Inventoteca/Alarma_Mochila/capturas y fotos/abrir manage pallete.png

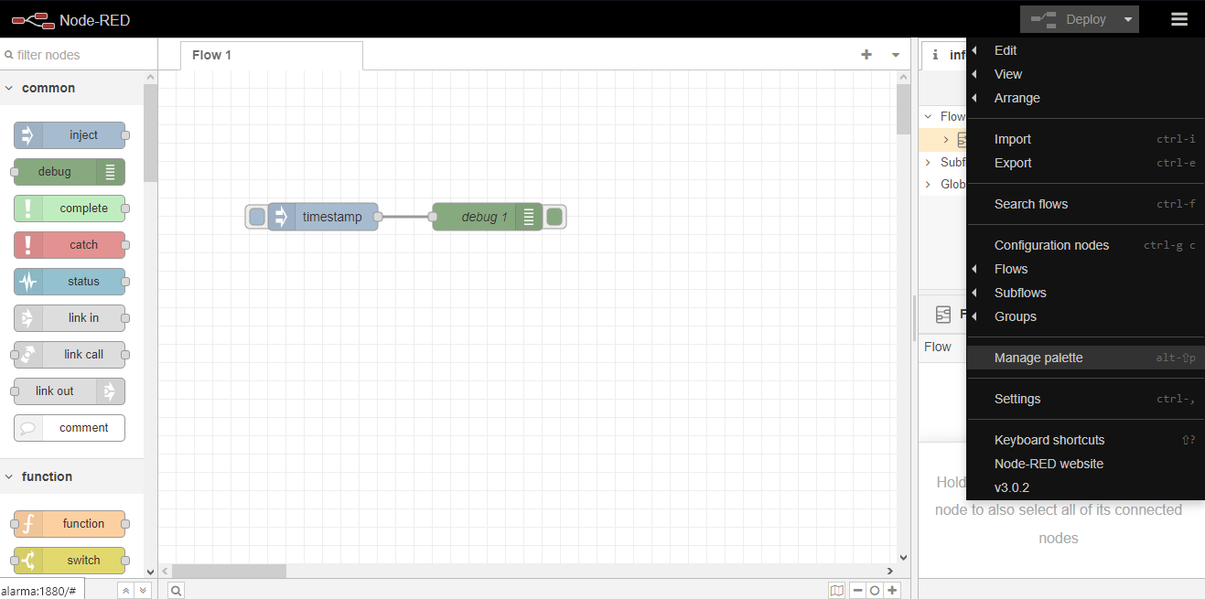
capturas y fotos/abrir manage pallete.png
