Inventoteca/Alarma_Mochila/capturas y fotos/arduino ejemplo esp32 ble.png

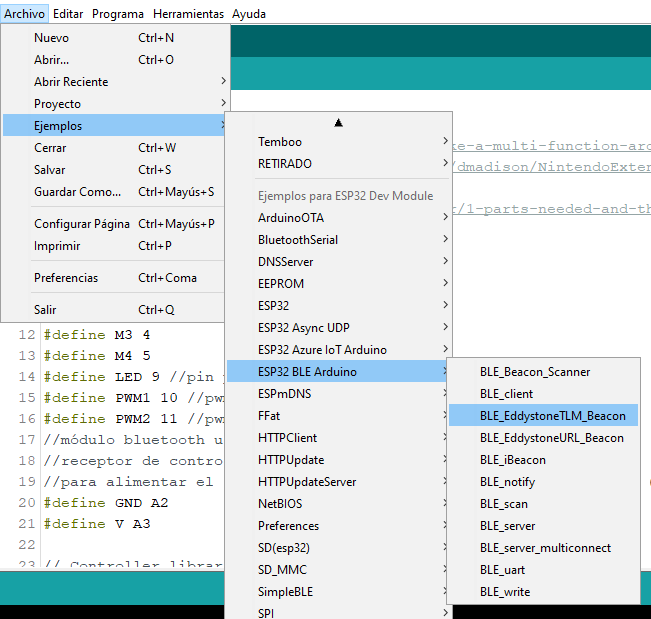
capturas y fotos/arduino ejemplo esp32 ble.png
