Inventoteca/Alarma_Mochila/capturas y fotos/config serial port 1.png

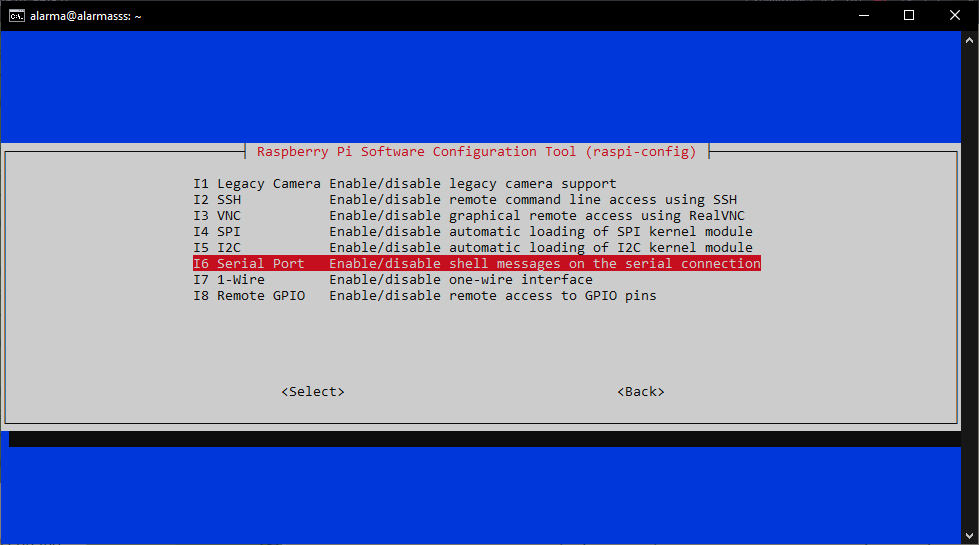
capturas y fotos/config serial port 1.png
