Inventoteca/Alarma_Mochila/capturas y fotos/config serial port 2.png

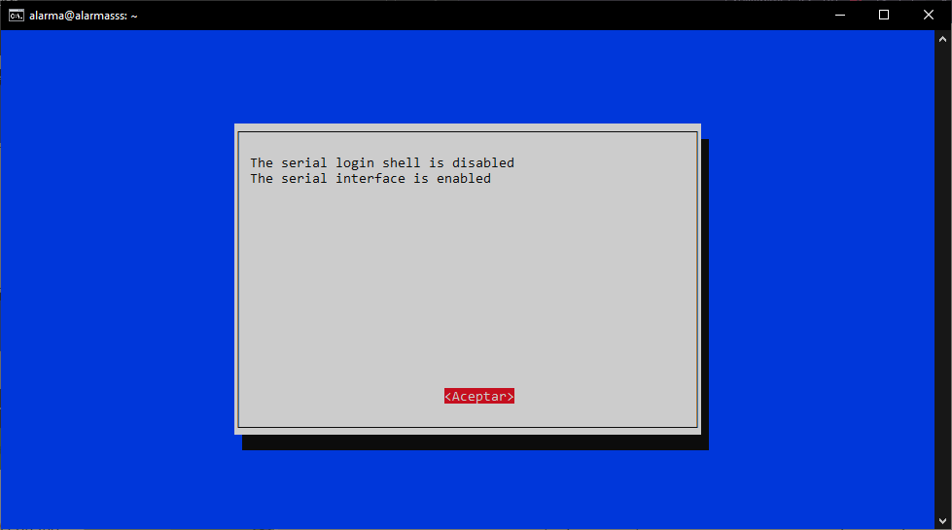
capturas y fotos/config serial port 2.png
