Inventoteca/Alarma_Mochila/capturas y fotos/configurar red en pc 2.png

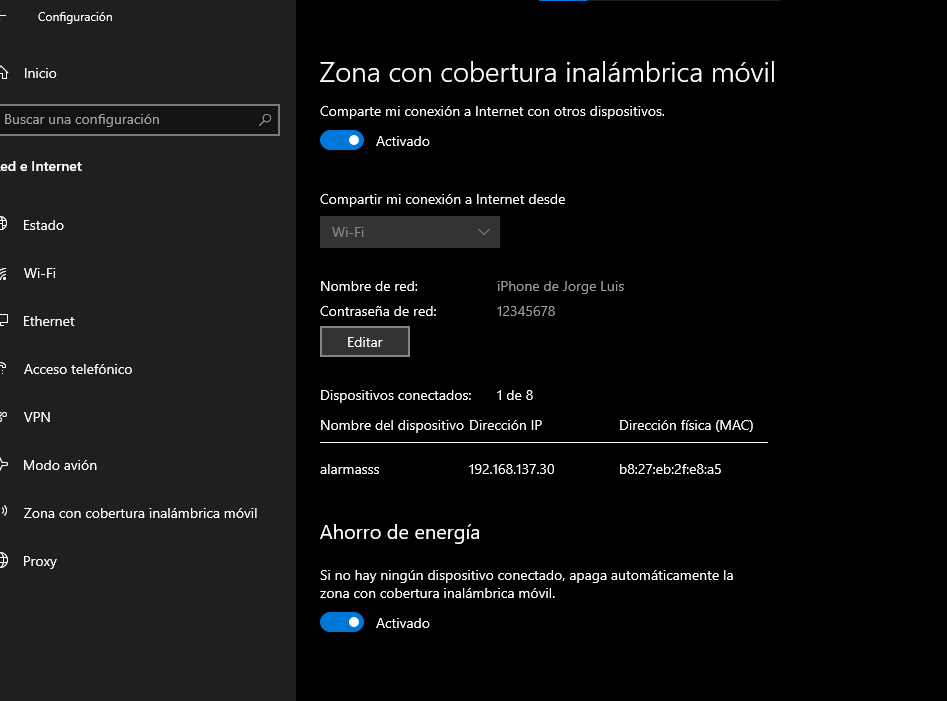
capturas y fotos/configurar red en pc 2.png
