Inventoteca/Alarma_Mochila/capturas y fotos/corriente 1.jpeg

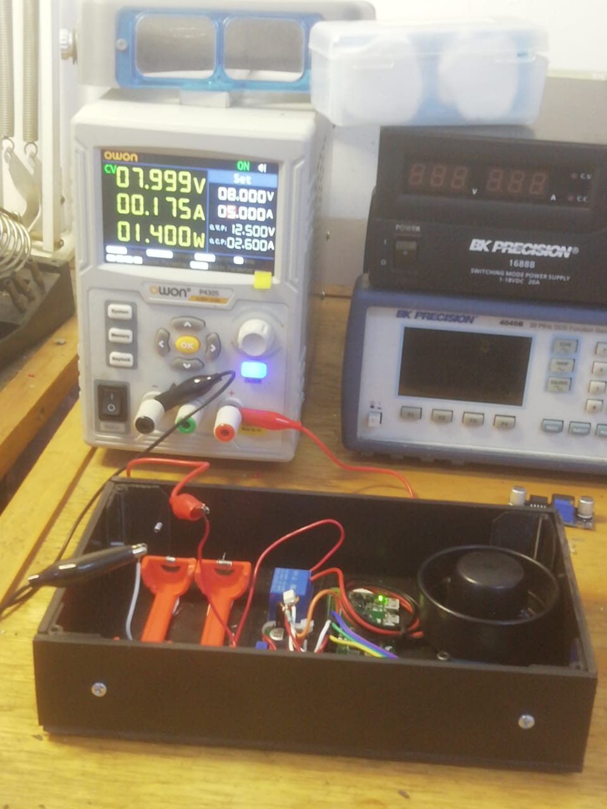
capturas y fotos/corriente 1.jpeg
