Inventoteca/Alarma_Mochila/capturas y fotos/flow.png

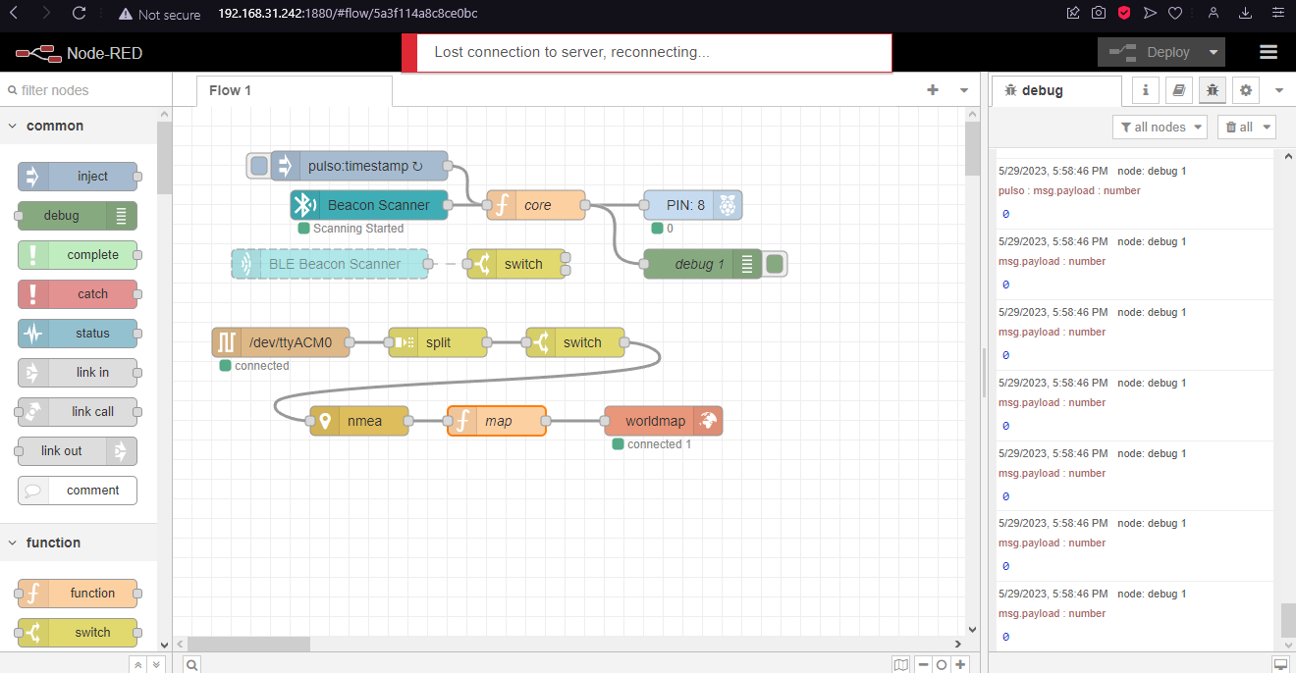
capturas y fotos/flow.png
