Inventoteca/Alarma_Mochila/capturas y fotos/flujo 2023-06-03.png

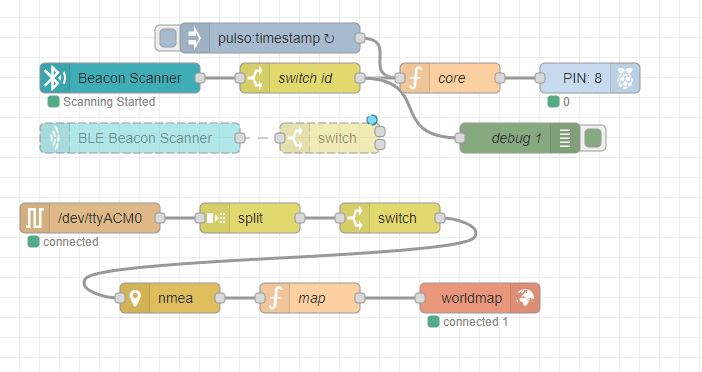
capturas y fotos/flujo 2023-06-03.png
