Inventoteca/Alarma_Mochila/capturas y fotos/instalando beacon scanner.png

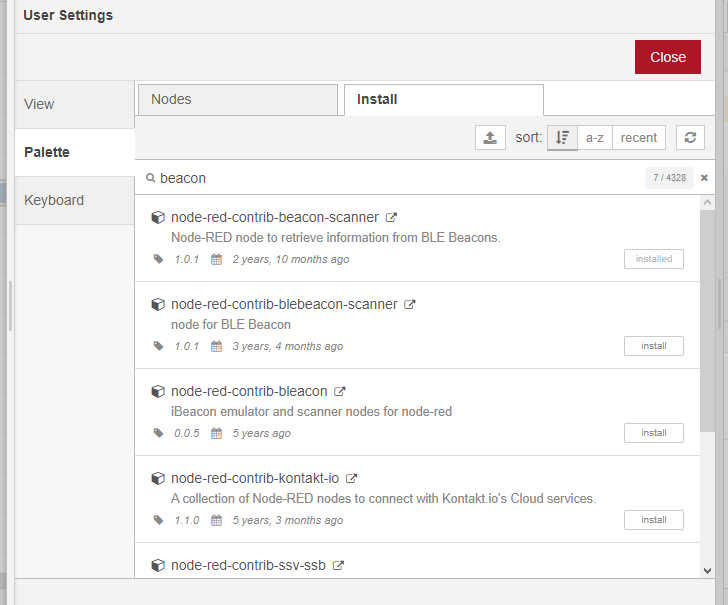
capturas y fotos/instalando beacon scanner.png
