Inventoteca/Alarma_Mochila/capturas y fotos/mapa en celular.png

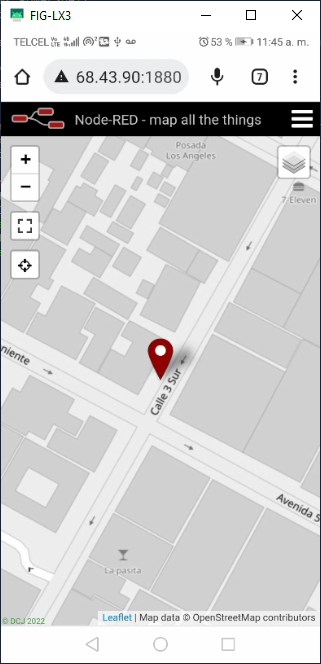
capturas y fotos/mapa en celular.png
